abersailbot/bobalong/control-system/src/sensors/compass.cpp

/*
	compass.cpp

	Provides functions for interacting with Bobalong's HMC6343 electronic compass

	This code is released under the terms of the LGPLv3 licence.
 */

#include "compass.h"
#include "Arduino.h"
#include "Wire.h"
#include "../utils.h"

#define HMC6343_ADDRESS 			0x19 // I2C device address
#define HMC6343_BEARING_REG 		0x50

#define I2C_TIMEOUT_MS 				2000

////////////////////////////////////////////////////////////////////////////////
void HMC6343_initialise() {
	Wire.begin();
	debug_print("I2C setup", DEBUG_LEVEL_IMPORTANT);
	delay(500);
}


////////////////////////////////////////////////////////////////////////////////
CompassData HMC6343_read_data() {
	byte high, low;
	unsigned long time_out;

	Serial.println("Setting Register");
	// Select the bearing register to be read
	Wire.beginTransmission(HMC6343_ADDRESS);
	Wire.write(HMC6343_BEARING_REG);
	Wire.endTransmission();

	Serial.println("Request data");
	// requests 6 bytes which will include bearing, pitch and roll
	Wire.requestFrom(HMC6343_ADDRESS, 6, true);

	 // wait for the data or time out
	time_out = millis() + I2C_TIMEOUT_MS;
	while(Wire.available() < 6) {
		if(millis() > time_out) {
			debug_print("Compass timed out!", DEBUG_LEVEL_CRITICAL);
			return CompassData();
		}
	}

	CompassData data;

	data.bearing = ((Wire.read() << 8)+ Wire.read()) / 10;
	data.pitch = ((Wire.read() << 8)+ Wire.read()) / 10;
	data.roll = ((Wire.read() << 8)+ Wire.read()) / 10;

	return data;
}
